Tom-Michiels/TiltBox/pictures/IMG_2047.jpeg

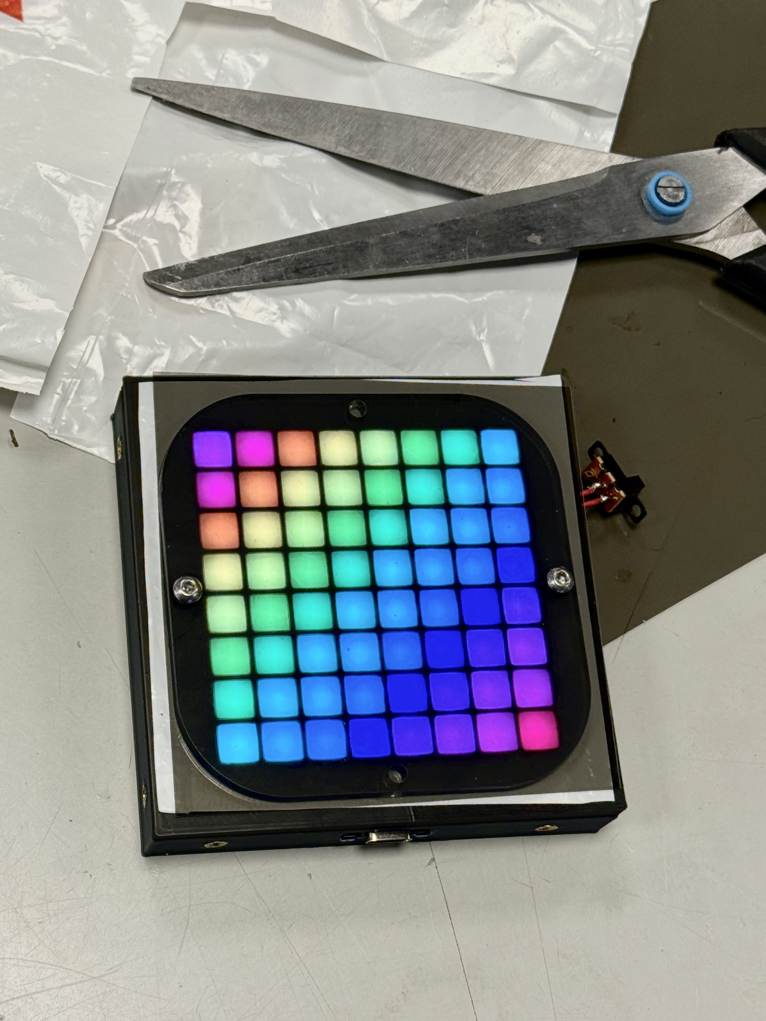
pictures/IMG_2047.jpeg
