Tom-Michiels/TiltBox/pictures/IMG_2048.jpeg

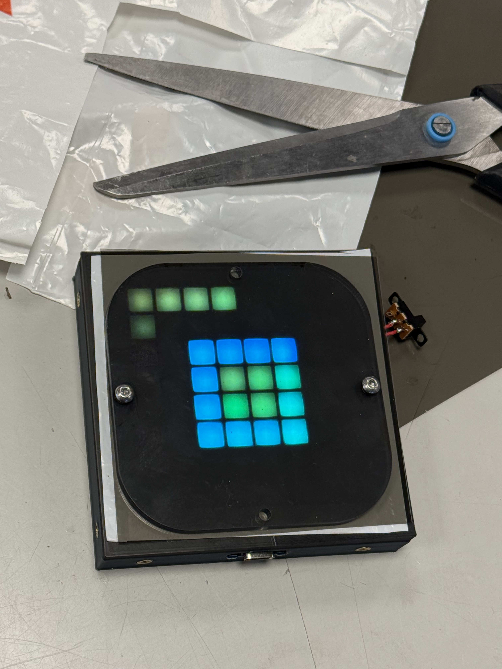
pictures/IMG_2048.jpeg
