Tom-Michiels/TiltBox/pictures/IMG_2049.jpeg

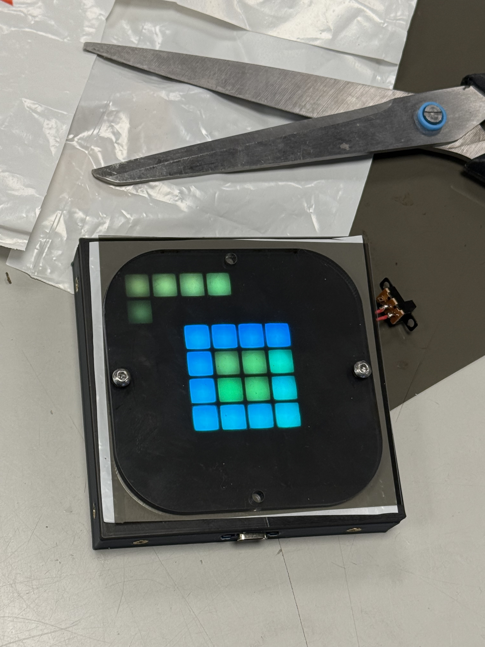
pictures/IMG_2049.jpeg
