Tom-Michiels/TiltBox/pictures/IMG_2050.jpeg

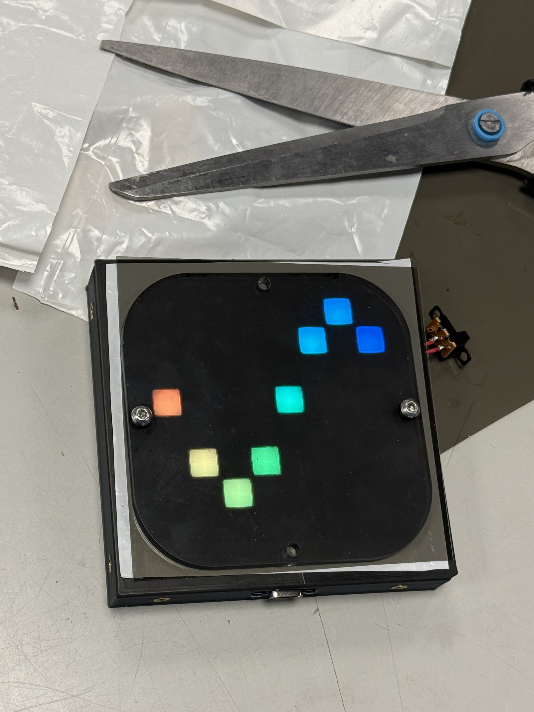
pictures/IMG_2050.jpeg
