Tom-Michiels/TiltBox/pictures/IMG_2052.jpeg

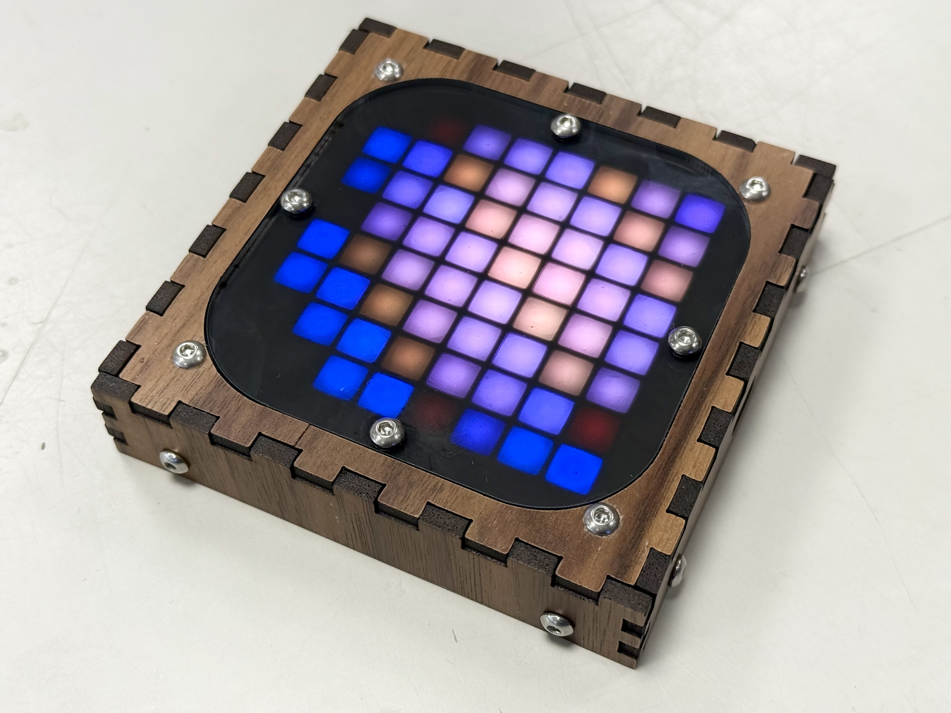
pictures/IMG_2052.jpeg
