Tom-Michiels/TiltBox/pictures/IMG_2053.jpeg

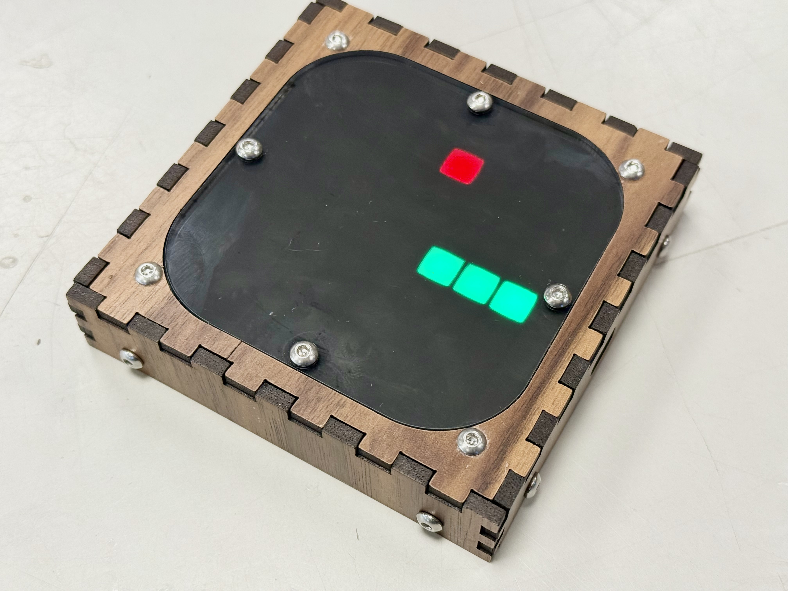
pictures/IMG_2053.jpeg
