Tom-Michiels/TiltBox/pictures/IMG_2054.jpeg

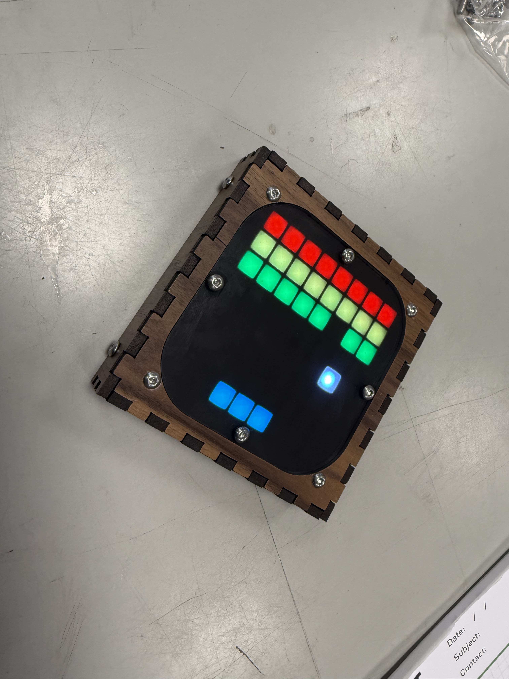
pictures/IMG_2054.jpeg
