Tom-Michiels/TiltBox/pictures/IMG_2055.jpeg

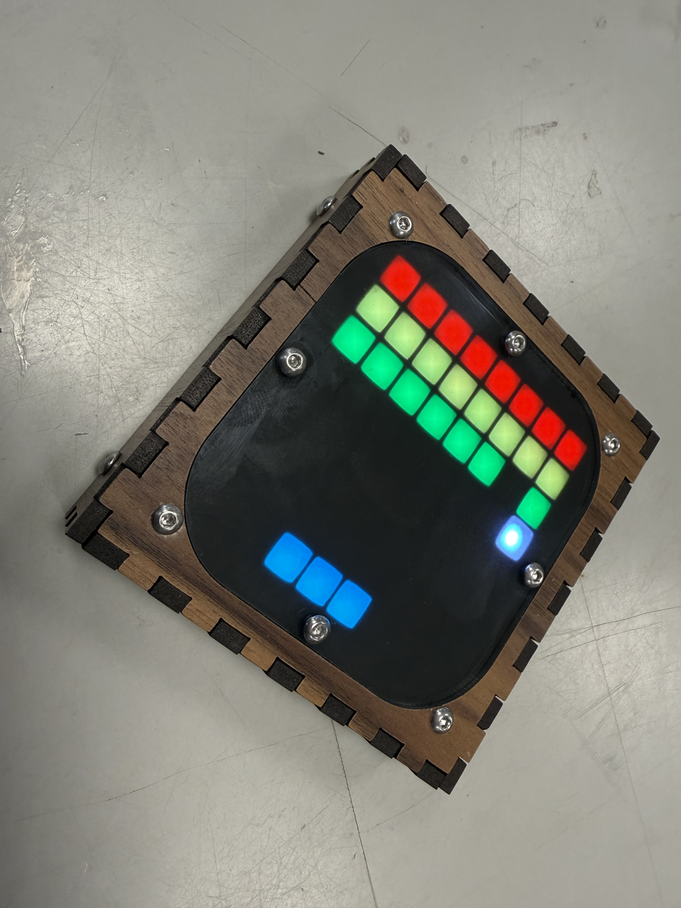
pictures/IMG_2055.jpeg
