Tom-Michiels/TiltBox/pictures/IMG_2056.jpeg

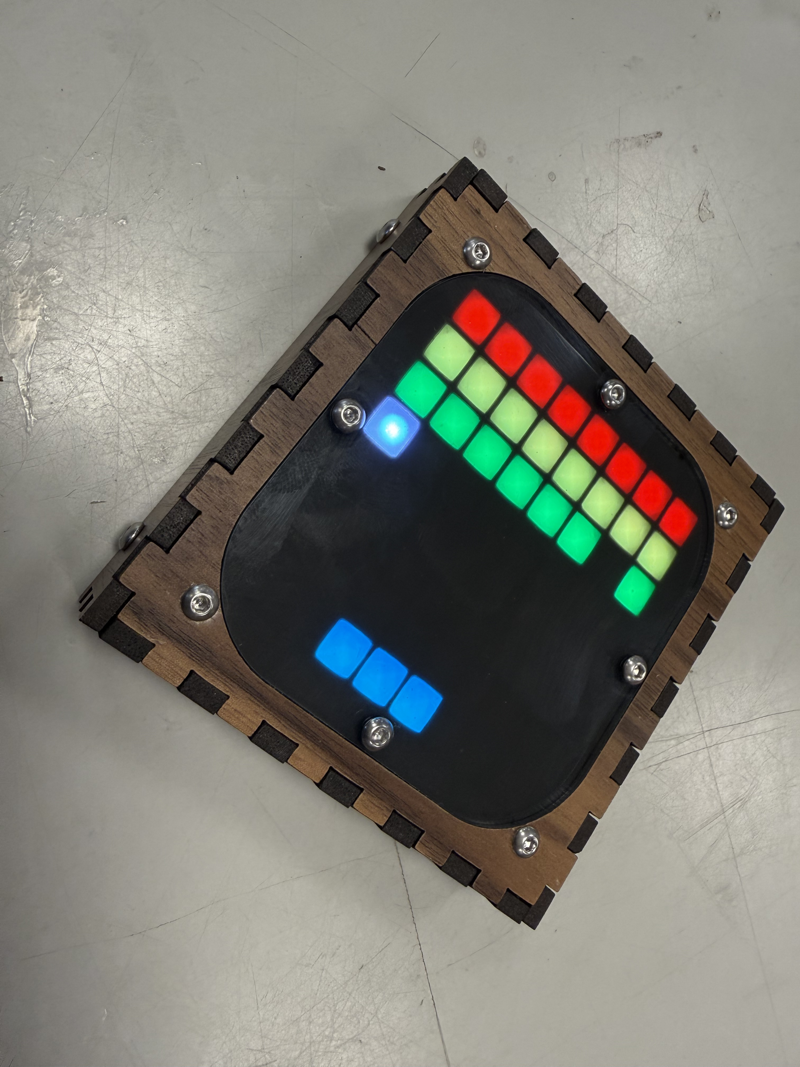
pictures/IMG_2056.jpeg
