Tom-Michiels/TiltBox/pictures/IMG_2057.jpeg

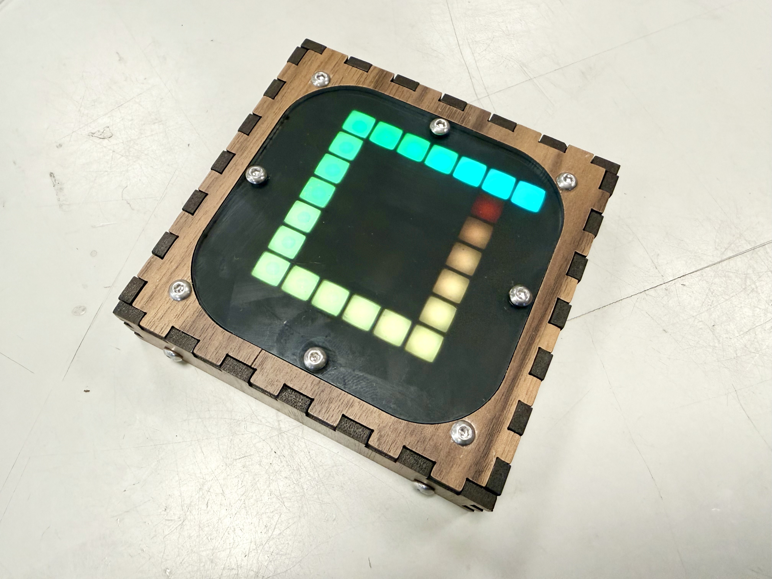
pictures/IMG_2057.jpeg
